MattisLind/IPCMemoryExpansion/Software/STM32CubeIDE/workspace_1.7.0/HP IPC Memory Expansion/Core/Inc/main.h

#define LED_RED_Pin GPIO_PIN_6
#define LED_RED_GPIO_Port GPIOG
#define LED_YELLOW_Pin GPIO_PIN_7
#define LED_YELLOW_GPIO_Port GPIOG
#define LED_GREEN_Pin GPIO_PIN_8
#define LED_GREEN_GPIO_Port GPIOG
#define RY_WAIT_Pin GPIO_PIN_6
#define RY_WAIT_GPIO_Port GPIOD
#define STM32_ENABLE_Pin GPIO_PIN_13
#define STM32_ENABLE_GPIO_Port GPIOG
